CrusaderSVK287/Rpi-Pico-controller-for-OpenRails/CAD/VoltMeter.FCStd

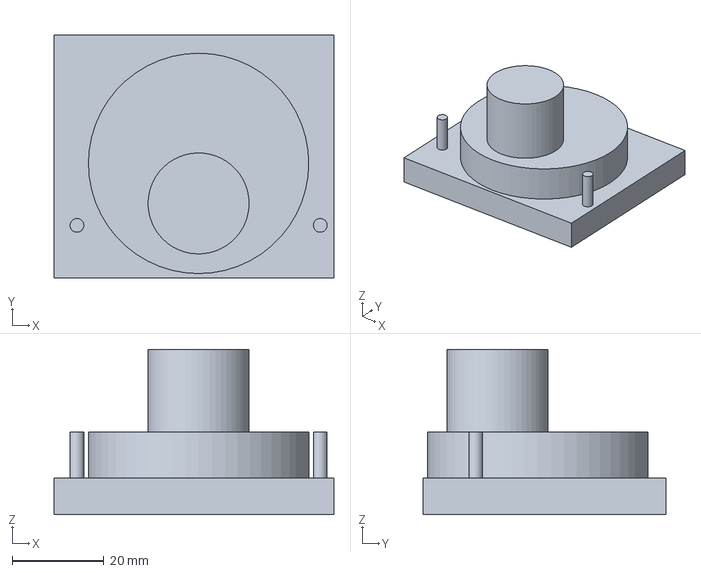
[picture p15: CAD file, 2025-12-12]
CAD/VoltMeter.FCStd
61.0 x 53.0 x 36.0 mm
