CrusaderSVK287/Rpi-Pico-controller-for-OpenRails/CAD/LeverSlotDirection.FCStd

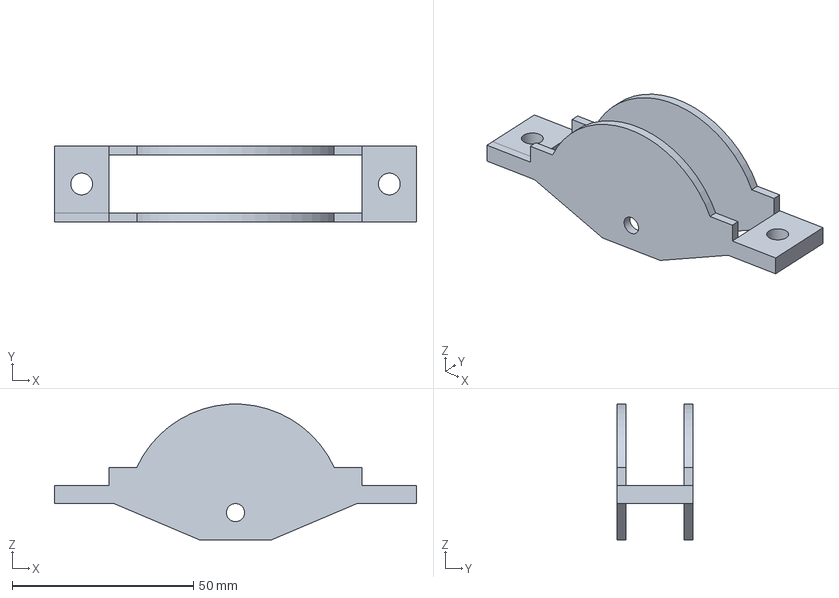
[picture p16: CAD file, 2025-12-12]
CAD/LeverSlotDirection.FCStd
100.0 x 21.0 x 37.4 mm
