CrusaderSVK287/Rpi-Pico-controller-for-OpenRails/CAD/SwtichRotary.FCStd

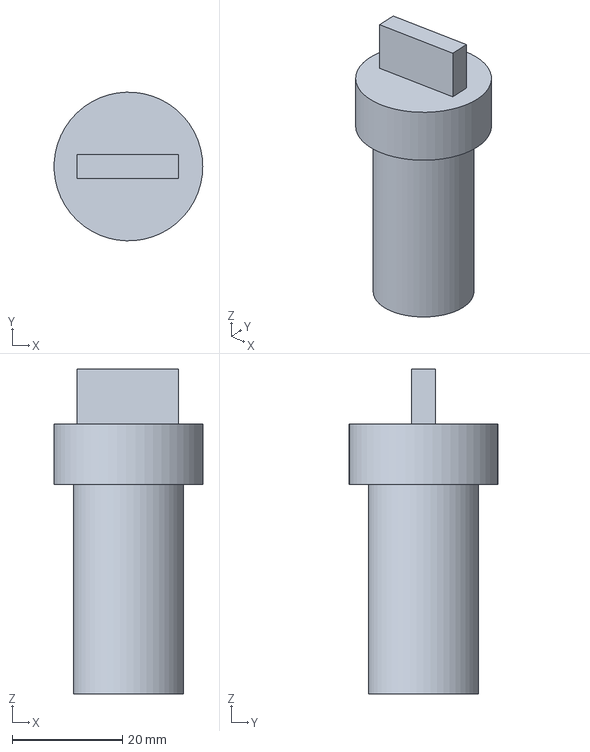
[picture p17: CAD file, 2025-12-12]
CAD/SwtichRotary.FCStd
27.0 x 27.0 x 59.0 mm
