CrusaderSVK287/Rpi-Pico-controller-for-OpenRails/CAD/Potentiometer_B10K.FCStd

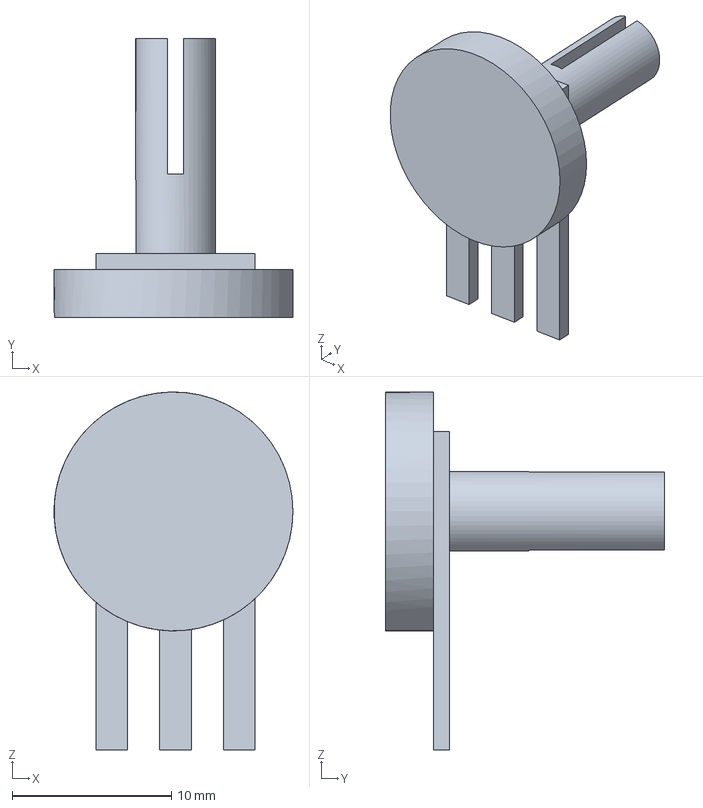
[picture p18: CAD file, 2025-12-12]
CAD/Potentiometer_B10K.FCStd
15.0 x 17.5 x 22.5 mm
