CrusaderSVK287/Rpi-Pico-controller-for-OpenRails/CAD/LeverDirection.FCStd

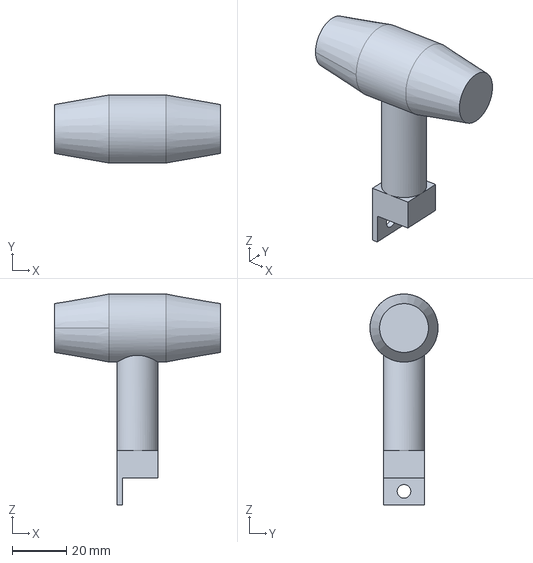
[picture p19: CAD file, 2025-12-12]
CAD/LeverDirection.FCStd
61.0 x 25.0 x 77.5 mm
