CrusaderSVK287/Rpi-Pico-controller-for-OpenRails/CAD/LeverThrottle.FCStd

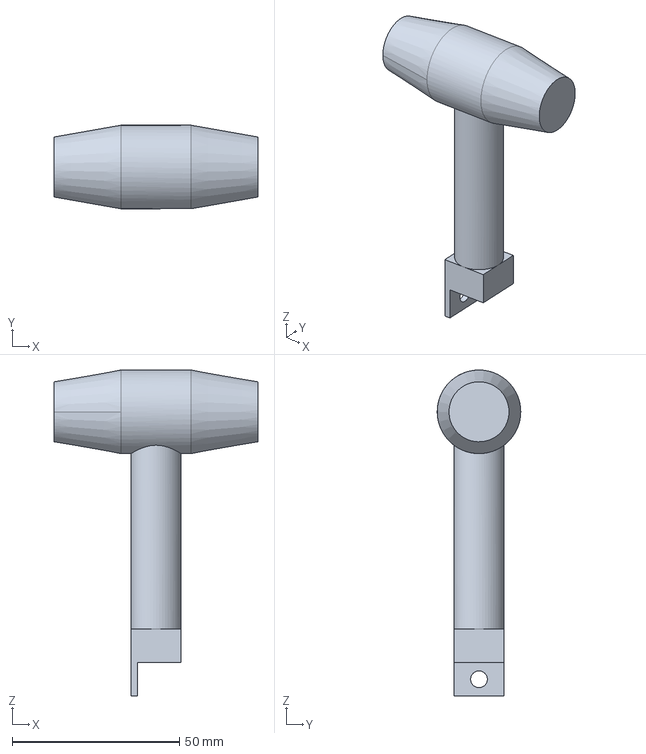
[picture p20: CAD file, 2025-12-12]
CAD/LeverThrottle.FCStd
61.0 x 25.0 x 97.5 mm
