CrusaderSVK287/Rpi-Pico-controller-for-OpenRails/src/tusb_config.h

#ifndef _TUSB_CONFIG_H_
#define _TUSB_CONFIG_H_

#define CFG_TUSB_MCU             OPT_MCU_RP2040
#ifdef CFG_TUSB_OS
  #undef CFG_TUSB_OS
#endif
#define CFG_TUSB_OS              OPT_OS_NONE
#define CFG_TUSB_RHPORT0_MODE    OPT_MODE_DEVICE

#define CFG_TUD_ENDPOINT0_SIZE   64

// Enable HID
#define CFG_TUD_HID              1
#define CFG_TUD_HID_EP_BUFSIZE   64

#endif
